Xerxes3rd/Twin-Stick-Controller/Reference Images/Control Panel Close Up.jpg

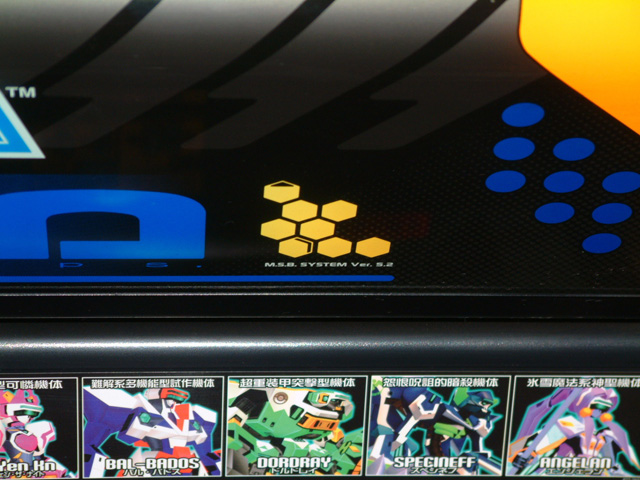
Reference Images/Control Panel Close Up.jpg
