Xerxes3rd/Twin-Stick-Controller/Reference Images/Dreamcast Twin Stick.jpg

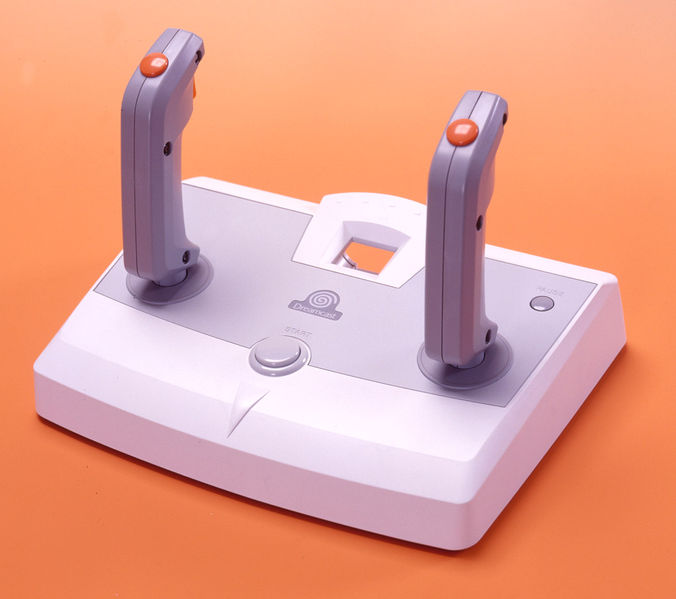
Reference Images/Dreamcast Twin Stick.jpg
