Xerxes3rd/Twin-Stick-Controller/Reference Images/Virtual On Arcade Control Panel Secondary.jpg

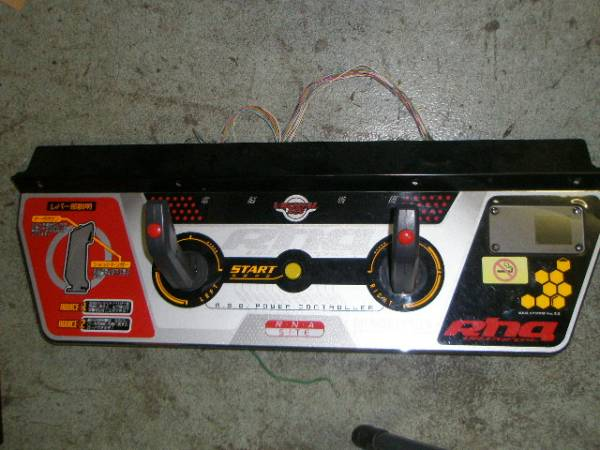
Reference Images/Virtual On Arcade Control Panel Secondary.jpg
