Xerxes3rd/Twin-Stick-Controller/Reference Images/Virtual On Force Arcade Control Panel 1.jpg

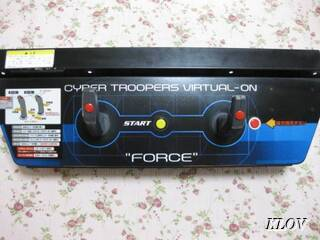
Reference Images/Virtual On Force Arcade Control Panel 1.jpg
