Xerxes3rd/Twin-Stick-Controller/Reference Images/Virtual On Force Arcade Control Panel 2.jpg

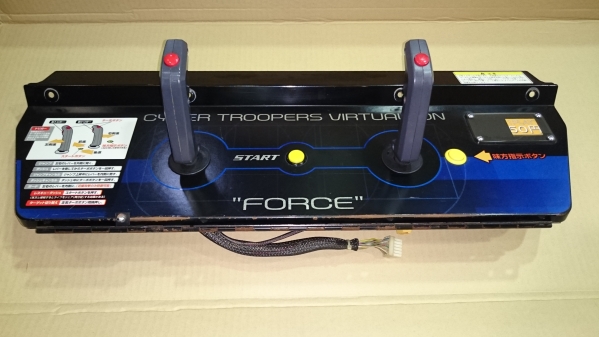
Reference Images/Virtual On Force Arcade Control Panel 2.jpg
