Xerxes3rd/Twin-Stick-Controller/Reference Images/Virtual On Oratorio Tangram Control Panel.jpg

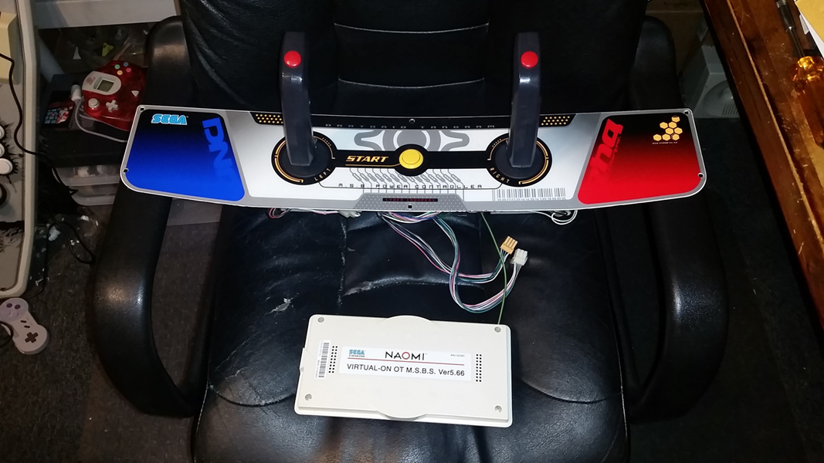
Reference Images/Virtual On Oratorio Tangram Control Panel.jpg
