Xerxes3rd/Twin-Stick-Controller/Reference Images/Virtual On Oratorio Tangram Control Panels 3.jpg

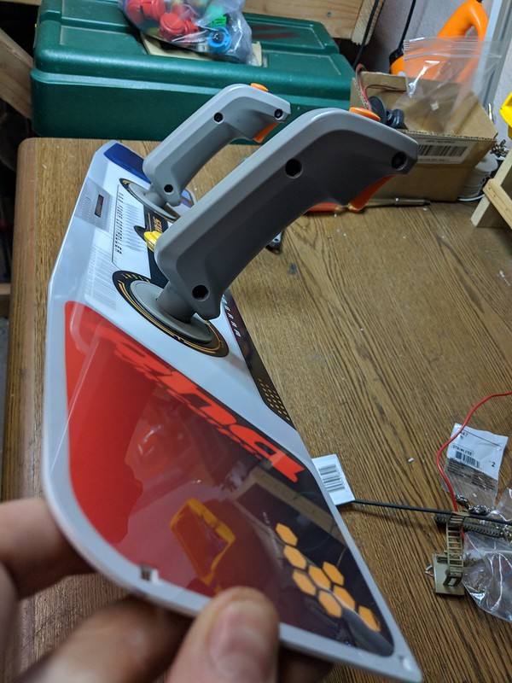
Reference Images/Virtual On Oratorio Tangram Control Panels 3.jpg
