Xerxes3rd/Twin-Stick-Controller/Reference Images/Virtual On Oratorio Tangram Control Panels Underside.jpg

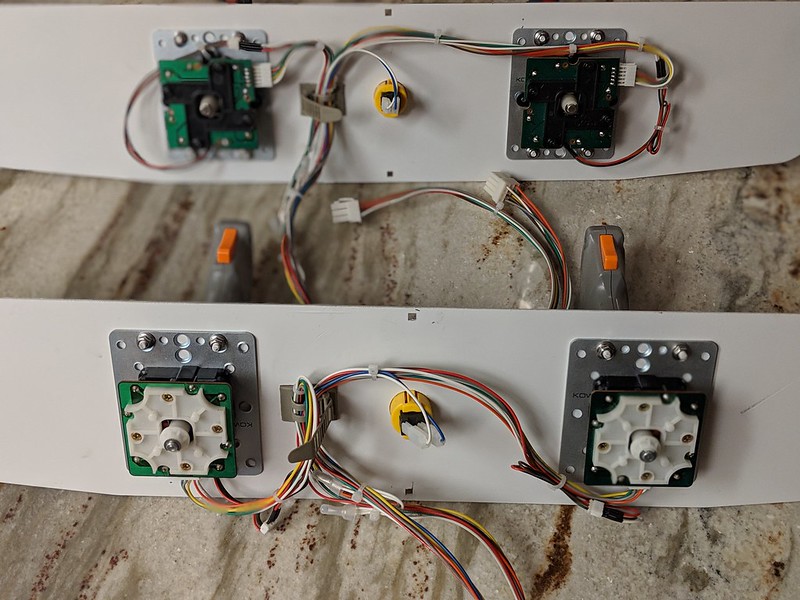
Reference Images/Virtual On Oratorio Tangram Control Panels Underside.jpg
