Xerxes3rd/Twin-Stick-Controller/Reference Images/Xbox Controller Map.jpg

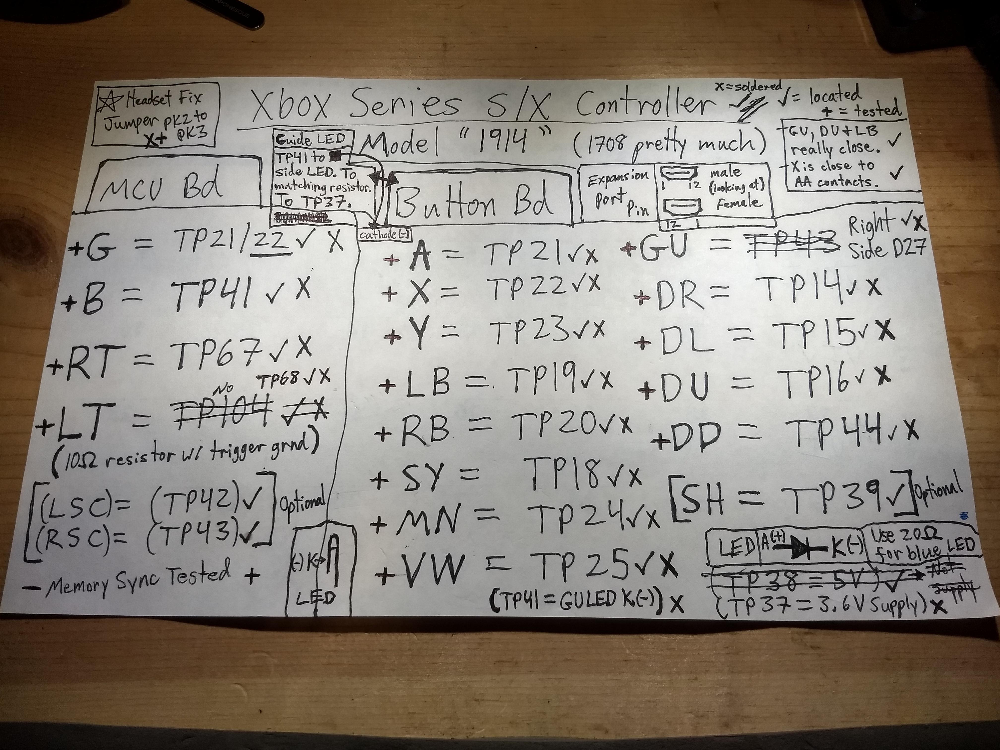
Reference Images/Xbox Controller Map.jpg
